Queens-Rocket-Engineering-Team/av-recovery/Firmware/GPS_Module/src/node.cpp

// node.cpp - GPS Module Application Logic
// References:
//   - u-blox SAM-M10Q Data Sheet & Integration Manual (UBX-22002218)
//   - AIM Network v0.7.0 Protocol Spec & Migration Plan (Decision D12/D14)
// MANDATORY PRE-FLIGHT CHECK: Make sure the SAM-M10Q GPS receiver is configured via u-center (u-blox UBX-CFG) for:
//   1. 10 Hz navigation update rate (matches kGpsActivePeriodMs = 100 ms)
//   2. High-G / Airborne dynamic model (Airborne <4g / Dynamic Model 8)

#include "node.h"

#include <Adafruit_NeoPixel.h>
#include <logger.h>
#include <Wire.h>
#include <TinyGPS++.h>
#include <aim_job.h>
#include <aim_flight_recorder.h>

static constexpr uint8_t  kGpsReadChunkBytes    = 64U;
static constexpr uint32_t kGpsNoDataWarnAfterMs = 5000U;

static TinyGPSPlus s_parser;
static bool s_hasValidTime = false;
static bool s_hasValidLocation = false;
static char s_readableTimeStr[20] = "N/A";
static int32_t s_lat1e7 = 0;
static int32_t s_lon1e7 = 0;
static int32_t s_altMeters = 0;

static bool s_gpsI2cFailed = false;
static bool s_gpsNoData = false;
static bool s_lowPower = false;
static bool s_loggedNoDataWarn = false;
static bool s_loggedNoLocWarn = false;

static aim::Job s_i2cErrorLogJob(5000U);     // 0.2 Hz error log rate
static aim::Job s_coordTxJob(100U);  // 10 Hz CAN tx
static aim::Job s_flashLogJob(100U); // 10 Hz flight log
static aim::Job s_satTxJob(5000U);           // 0.2 Hz satellite count tx

static Adafruit_NeoPixel s_rgbLeds(1U, pins::kRgbData, NEO_GRB + NEO_KHZ800);

static int32_t rawDegreesTo1e7(const RawDegrees& raw) {
  int32_t deg1e7 = static_cast<int32_t>(raw.deg) * 10000000L + static_cast<int32_t>(raw.billionths / 100U);
  return raw.negative ? -deg1e7 : deg1e7;
}

static void updateLed(aim::NodeState state) {
  uint8_t color = 3; // blue default (searching)
  if (state == aim::NodeState::Fault) { color = 2; } // red
  else if (state == aim::NodeState::Nominal && s_hasValidLocation) { color = 1; } // green

  static uint8_t s_lastColor = 0xFF;
  if (color == s_lastColor) return;
  s_lastColor = color;

  uint8_t r = 0, g = 0, b = 0;
  switch (color) { case 1: g = 255; break; case 2: r = 255; break; default: b = 255; break; }
  s_rgbLeds.setPixelColor(0, s_rgbLeds.Color(r, g, b));
  s_rgbLeds.show();
}

static uint32_t s_lastFixSentenceMs = 0;
static uint32_t s_fixDeltaMs = 0;

static void ubxChecksum(const uint8_t* f, size_t from, size_t to, uint8_t& a, uint8_t& b) {
  a = 0; b = 0;
  for (size_t i = from; i < to; i++) { a += f[i]; b += a; }
}

static size_t buildUbxFrame(uint8_t cls, uint8_t id, const uint8_t* p, uint8_t n, uint8_t* out) {
  out[0] = 0xB5; out[1] = 0x62; out[2] = cls; out[3] = id;
  out[4] = static_cast<uint8_t>(n & 0xFF);
  out[5] = static_cast<uint8_t>((n >> 8) & 0xFF);
  memcpy(out + 6, p, n);
  uint8_t a, b;
  ubxChecksum(out, 2, 6 + n, a, b);
  out[6 + n] = a; out[7 + n] = b;
  return 8 + n;
}

static bool i2cWriteGps(const uint8_t* d, size_t n) {
  Wire.beginTransmission(static_cast<uint8_t>(pins::kGpsAddr));
  Wire.write(d, n);
  return (Wire.endTransmission() == 0);
}

static uint16_t gpsAvailableBytes() {
  Wire.beginTransmission(static_cast<uint8_t>(pins::kGpsAddr));
  Wire.write(static_cast<uint8_t>(0xFD));
  if (Wire.endTransmission(false) != 0) return 0;
  Wire.requestFrom(static_cast<int>(pins::kGpsAddr), 2);
  if (Wire.available() < 2) return 0;
  uint16_t hi = Wire.read(), lo = Wire.read();
  return (hi << 8) | lo;
}

static int gpsReadSingleByte() {
  Wire.beginTransmission(static_cast<uint8_t>(pins::kGpsAddr));
  Wire.write(static_cast<uint8_t>(0xFF));
  if (Wire.endTransmission(false) != 0) return -1;
  Wire.requestFrom(static_cast<int>(pins::kGpsAddr), 1);
  if (!Wire.available()) return -1;
  return Wire.read();
}

static bool waitForUbxAck(uint8_t expCls, uint8_t expId, uint32_t timeoutMs = 300) {
  const uint32_t start = millis();
  uint8_t state = 0, type = 0, cls = 0, id = 0;
  while (millis() - start < timeoutMs) {
    uint16_t avail = gpsAvailableBytes();
    while (avail-- > 0) {
      int b = gpsReadSingleByte();
      if (b < 0) break;
      switch (state) {
        case 0: state = (b == 0xB5) ? 1 : 0; break;
        case 1: state = (b == 0x62) ? 2 : 0; break;
        case 2: state = (b == 0x05) ? 3 : 0; break;
        case 3: if (b == 0x01 || b == 0x00) { type = static_cast<uint8_t>(b); state = 4; } else state = 0; break;
        case 4: state = (b == 0x02) ? 5 : 0; break;
        case 5: state = (b == 0x00) ? 6 : 0; break;
        case 6: cls = static_cast<uint8_t>(b); state = 7; break;
        case 7:
          id = static_cast<uint8_t>(b); state = 0;
          if (cls == expCls && id == expId) return (type == 0x01);
          break;
      }
    }
  }
  return false;
}

static bool setCfgValU1(uint32_t key, uint8_t val) {
  uint8_t p[9] = {0x00, 0x03, 0x00, 0x00, static_cast<uint8_t>(key), static_cast<uint8_t>(key >> 8), static_cast<uint8_t>(key >> 16), static_cast<uint8_t>(key >> 24), val};
  uint8_t f[24];
  size_t len = buildUbxFrame(0x06, 0x8A, p, sizeof(p), f);
  if (!i2cWriteGps(f, len)) return false;
  return waitForUbxAck(0x06, 0x8A);
}

static bool setCfgValU2(uint32_t key, uint16_t val) {
  uint8_t p[10] = {0x00, 0x03, 0x00, 0x00, static_cast<uint8_t>(key), static_cast<uint8_t>(key >> 8), static_cast<uint8_t>(key >> 16), static_cast<uint8_t>(key >> 24), static_cast<uint8_t>(val), static_cast<uint8_t>(val >> 8)};
  uint8_t f[24];
  size_t len = buildUbxFrame(0x06, 0x8A, p, sizeof(p), f);
  if (!i2cWriteGps(f, len)) return false;
  return waitForUbxAck(0x06, 0x8A);
}

static bool configureGpsRuntime() {
  bool ok = true;
  ok &= setCfgValU2(0x30210001, 100);  // CFG-RATE-MEAS = 100ms (10 Hz)
  ok &= setCfgValU2(0x30210002, 1);    // CFG-RATE-NAV  = 1 (1 fix/meas)
  ok &= setCfgValU1(0x20110021, 8);    // CFG-NAVSPG-DYNMODEL = 8 (Airborne <4g)
  ok &= setCfgValU1(0x10510002, 1);    // CFG-I2C-EXTENDEDTIMEOUT = true
  ok &= setCfgValU1(0x1031001F, 1);    // GPS enable
  ok &= setCfgValU1(0x10310021, 1);    // GALILEO enable
  ok &= setCfgValU1(0x10310025, 0);    // GLONASS disable (for 10Hz limit)
  ok &= setCfgValU1(0x10310022, 0);    // BEIDOU disable
  ok &= setCfgValU1(0x10310020, 0);    // SBAS disable
  ok &= setCfgValU1(0x10310024, 0);    // QZSS disable
  return ok;
}

void nodeInit() {
  s_rgbLeds.begin();
  s_rgbLeds.setPixelColor(0, s_rgbLeds.Color(0, 0, 0));
  s_rgbLeds.show();

  Wire.setSCL(pins::kGpsScl);
  Wire.setSDA(pins::kGpsSda);
  Wire.begin();
  Wire.setClock(400000);  // Fast-Mode I2C clock speed (400 kHz)
  Wire.setTimeout(10U);   // 10 ms bus timeout protection

  if (configureGpsRuntime()) {
    LOG_INFO("SAM-M10Q configured: 10 Hz Airborne <4g (ACK verified)");
  } else {
    LOG_WARN("SAM-M10Q runtime config unconfirmed or NAK");
  }
}

void nodeUpdate(uint32_t nowMs) {
  updateLed(nodeCurrentState());

  Wire.beginTransmission(static_cast<uint8_t>(pins::kGpsAddr));
  Wire.write(0xFFU);
  const uint8_t txStatus = Wire.endTransmission(false);
  if (txStatus != 0U) {
    s_gpsI2cFailed = true;
    if (s_i2cErrorLogJob.due(nowMs)) {
      LOG_WARN("GPS I2C request failed status=%u", static_cast<unsigned>(txStatus));
    }
  } else {
    s_gpsI2cFailed = false;
    (void)Wire.requestFrom(static_cast<uint8_t>(pins::kGpsAddr), kGpsReadChunkBytes);
    for (uint8_t i = 0U; (i < kGpsReadChunkBytes) && (Wire.available() > 0); i++) {
      uint8_t b = static_cast<uint8_t>(Wire.read());
      // SAM-M10Q returns 0xFF when I2C stream FIFO is empty — do not feed 0xFF pad bytes to NMEA parser.
      if (b != 0xFFU) {
        (void)s_parser.encode(static_cast<char>(b));
      }
    }
  }

  if (nowMs > kGpsNoDataWarnAfterMs && s_parser.charsProcessed() < 10UL) {
    s_gpsNoData = true;
    if (!s_loggedNoDataWarn) {
      LOG_WARN("No GPS NMEA data detected yet");
      s_loggedNoDataWarn = true;
    }
  } else {
    s_gpsNoData = false;
  }

  if (!s_parser.time.isValid()) {
    s_hasValidTime = false;
  } else {
    if (!s_hasValidTime) {
      s_hasValidTime = true;
      LOG_DEBUG("GPS time lock acquired");
    }
    if (s_parser.time.isUpdated()) {
      if (s_lastFixSentenceMs > 0U) {
        s_fixDeltaMs = nowMs - s_lastFixSentenceMs;
      }
      s_lastFixSentenceMs = nowMs;

      snprintf(s_readableTimeStr, sizeof(s_readableTimeStr), "%02u:%02u:%02u.%02u",
               static_cast<unsigned>(s_parser.time.hour()),
               static_cast<unsigned>(s_parser.time.minute()),
               static_cast<unsigned>(s_parser.time.second()),
               static_cast<unsigned>(s_parser.time.centisecond()));
    }
  }

  if (!s_parser.location.isValid()) {
    s_hasValidLocation = false;
  } else {
    s_lon1e7 = rawDegreesTo1e7(s_parser.location.rawLng());
    s_lat1e7 = rawDegreesTo1e7(s_parser.location.rawLat());
    s_hasValidLocation = true;
  }

  if (s_parser.altitude.isValid()) {
    s_altMeters = static_cast<int32_t>(s_parser.altitude.meters()); // Whole meters MSL
  }
}

void nodeServiceLog(uint32_t nowMs, AimFlightRecorder& recorder) {
  if (!s_flashLogJob.due(nowMs)) return;
  if (!s_hasValidLocation) return;

  uint32_t rowData[4] = {
    nowMs,
    AimFlightRecorder::unsignify(s_lon1e7),
    AimFlightRecorder::unsignify(s_lat1e7),
    AimFlightRecorder::unsignify(s_altMeters)
  };

  recorder.writeRow(rowData);
}

void nodeServiceCanTx(uint32_t nowMs, AimNetwork& aim) {
  // 1. High-frequency position broadcast (10 Hz in flight / 1 Hz on pad)
  if (s_coordTxJob.due(nowMs)) {
    if (!s_hasValidLocation) {
      if (!s_loggedNoLocWarn) {
        LOG_WARN("GPS coordinate TX paused until location is valid");
        s_loggedNoLocWarn = true;
      }
    } else {
      s_loggedNoLocWarn = false;
      aim::Msg gpsPos = {};
      gpsPos.cls = aim::Class::Sensor;
      gpsPos.subject = aim::subject::GpsPosition;
      gpsPos.setGpsPosition(s_lon1e7, s_lat1e7);
      if (!aim.send(gpsPos)) {
        LOG_ERROR("GPS coord TX failed");
      }
    }
  }

  // 2. Low-frequency satellite count broadcast (once every 5 seconds)
  if (s_satTxJob.due(nowMs) && s_parser.satellites.isValid()) {
    aim::Msg satsMsg = {};
    satsMsg.cls = aim::Class::Sensor;
    satsMsg.subject = aim::subject::GpsNumSats;
    satsMsg.setSensorValue(static_cast<int32_t>(s_parser.satellites.value()));
    (void)aim.send(satsMsg);
  }
}


void nodeOnRx(const aim::Msg& m, uint32_t nowMs) {
  (void)nowMs;
  if (m.cls == aim::Class::Event) {
    if (m.subject == aim::subject::LowPower) {
      s_lowPower = (m.b[0] == 1U);
      LOG_DEBUG("GPS low power state updated: %d", s_lowPower);
    }
  }
}

aim::NodeState nodeCurrentState() {
  return s_gpsI2cFailed ? aim::NodeState::Fault : aim::NodeState::Nominal;
}

uint16_t nodeErrorBits() {
  uint16_t bits = 0U;
  if (s_gpsI2cFailed) bits |= (1U << 0);
  if (s_gpsNoData)    bits |= (1U << 1);
  return bits;
}

#ifndef FLIGHT_BUILD
static void hookGpsSnapshot(Stream& out) {
  out.print("gps timeValid(parser/state)=");
  out.print(s_parser.time.isValid() ? 1 : 0);
  out.print("/");
  out.println(s_hasValidTime ? 1 : 0);

  out.print("gps locValid(parser/state)=");
  out.print(s_parser.location.isValid() ? 1 : 0);
  out.print("/");
  out.println(s_hasValidLocation ? 1 : 0);

  out.print("gps sats(valid/count)=");
  out.print(s_parser.satellites.isValid() ? 1 : 0);
  out.print("/");
  out.println(static_cast<unsigned long>(s_parser.satellites.value()));

  out.print("UTC Time=");
  out.println(s_readableTimeStr);

  out.print("lon1e7=");
  out.println(static_cast<long>(s_lon1e7));
  out.print("lat1e7=");
  out.println(static_cast<long>(s_lat1e7));
  out.print("altMeters=");
  out.println(static_cast<long>(s_altMeters));

  out.print("txPeriodMs=");
  out.println(static_cast<unsigned long>(s_coordTxJob.periodMs));
  out.print("logPeriodMs=");
  out.println(static_cast<unsigned long>(s_flashLogJob.periodMs));
}

static void hookGpsParserStats(Stream& out) {
  out.print("chars=");
  out.println(static_cast<unsigned long>(s_parser.charsProcessed()));
  out.print("sentencesWithFix=");
  out.println(static_cast<unsigned long>(s_parser.sentencesWithFix()));
  out.print("checksum pass/fail=");
  out.print(static_cast<unsigned long>(s_parser.passedChecksum()));
  out.print("/");
  out.println(static_cast<unsigned long>(s_parser.failedChecksum()));
  out.print("fixRate=");
  out.print(static_cast<unsigned long>(s_fixDeltaMs));
  out.print(" ms (");
  if (s_fixDeltaMs > 0U) {
    out.print(1000.0f / static_cast<float>(s_fixDeltaMs), 1);
    out.println(" Hz)");
  } else {
    out.println("N/A)");
  }
}

static const AimConsoleHook s_consoleHooks[] = {
  {'g', "gps snapshot", hookGpsSnapshot},
  {'p', "gps parser stats", hookGpsParserStats},
};

const AimConsoleHook* nodeConsoleHooks(uint8_t& count) {
  count = sizeof(s_consoleHooks) / sizeof(s_consoleHooks[0]);
  return s_consoleHooks;
}
#endif
