Queens-Rocket-Engineering-Team/av-recovery/Firmware/Altimeter_Module/src/node.h

#ifndef NODE_H
#define NODE_H

#include <Arduino.h>
#include <cstdint>

#include <aim_network.h>

#include "pinouts.h"

class AimFlightRecorder;

// Node-level identity and interface configuration.
namespace node {
constexpr char        kName[]     = "ALTIMETER_MODULE";
constexpr aim::Source kSource     = aim::Source::Altimeter;
constexpr uint32_t    kCanBaud    = 1000000U;
constexpr uint32_t    kSerialBaud = 38400U;
}  // namespace node
 
static constexpr uint8_t  kLogCols           = 12U;
static constexpr uint16_t kLogOriginRefresh  = 100U;
static constexpr uint32_t kLogMaxSize        = 0;
static const char* const  kLogHeaders[kLogCols] = {
  "time", "pressPa", "altCm", "imuAccX", "imuAccY", "imuAccZ", "gyroX", "gyroY", "gyroZ", "highAccX", "highAccY", "highAccZ"
};

// Application logic entry points.
void nodeInit();
void nodeUpdate(uint32_t nowMs);
void nodeServiceLog(uint32_t nowMs, AimFlightRecorder& recorder);
void nodeServiceCanTx(uint32_t nowMs, AimNetwork& aim);
void nodeOnRx(const aim::Msg& m, uint32_t nowMs);

aim::NodeState nodeCurrentState();
uint16_t nodeErrorBits();

#ifndef FLIGHT_BUILD
#include <aim_console.h>
const AimConsoleHook* nodeConsoleHooks(uint8_t& count);
#endif

#endif  // NODE_H
